dontsovcmc/waterius/Board/1.0-homemade/waterius-homemade-board.png

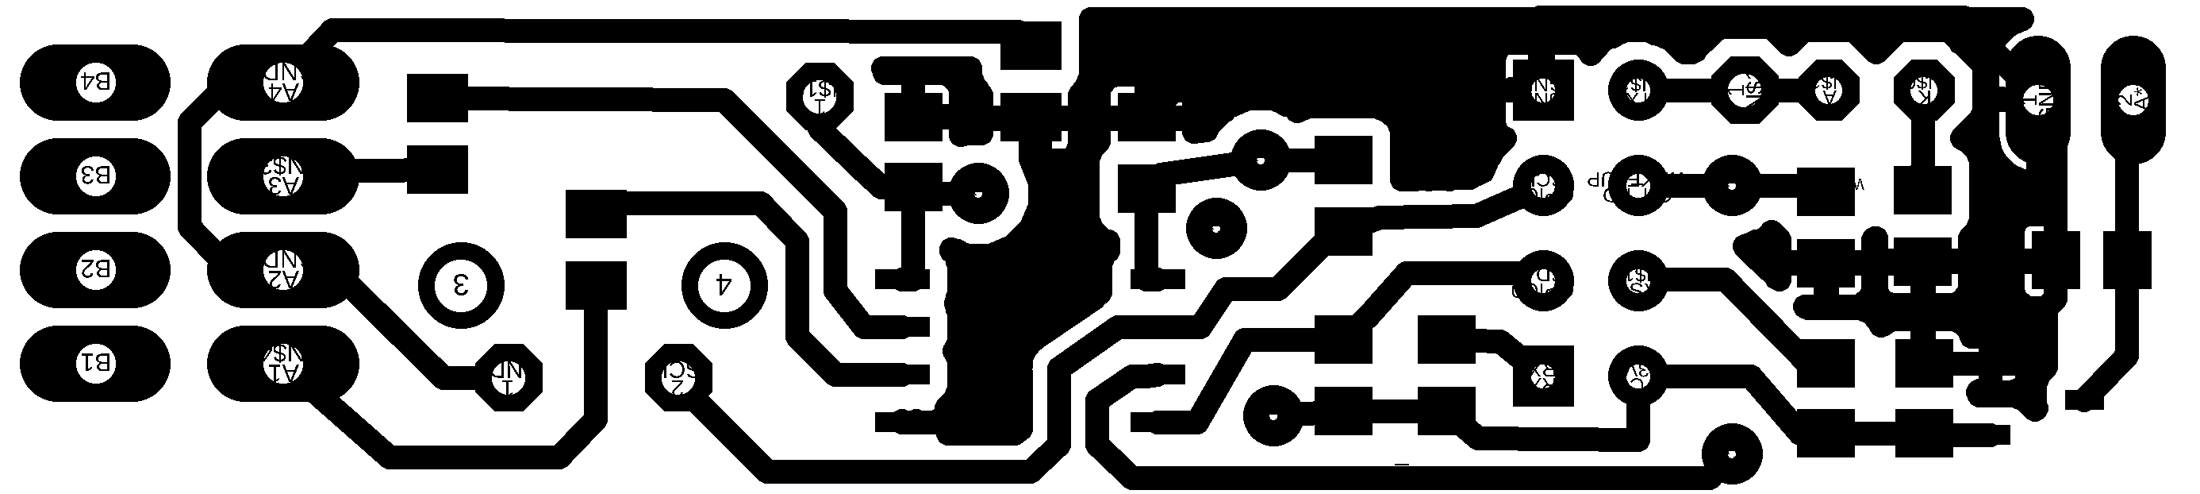
Board/1.0-homemade/waterius-homemade-board.png
