dontsovcmc/waterius/Board/2.0/waterius-factory-board2_top.jpg

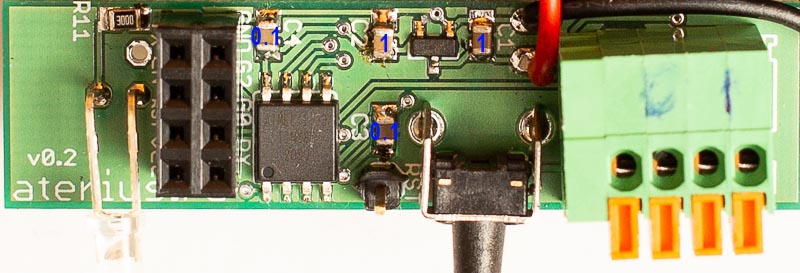
Board/2.0/waterius-factory-board2_top.jpg
