dontsovcmc/waterius/Board/3.0/waterius-factory-board3_top.jpg

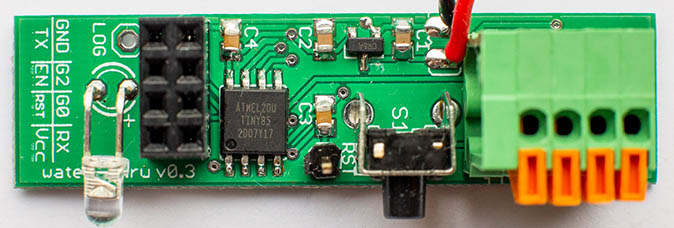
Board/3.0/waterius-factory-board3_top.jpg
