dontsovcmc/waterius/ESP8266/data/images/meter-cold-0.png

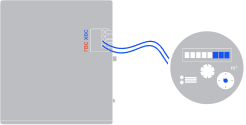
ESP8266/data/images/meter-cold-0.png
