dontsovcmc/waterius/ESP8266/data/images/meter-electro-0.png

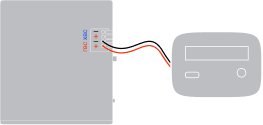
ESP8266/data/images/meter-electro-0.png
