dontsovcmc/waterius/ESP8266/data/images/meter-gas-0.png

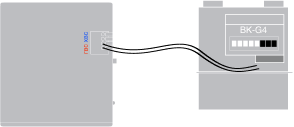
ESP8266/data/images/meter-gas-0.png
