dontsovcmc/waterius/files/11541426.png

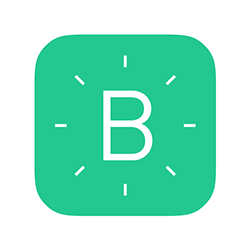
files/11541426.png
