dontsovcmc/waterius/files/esp8266-01s_mod.jpg

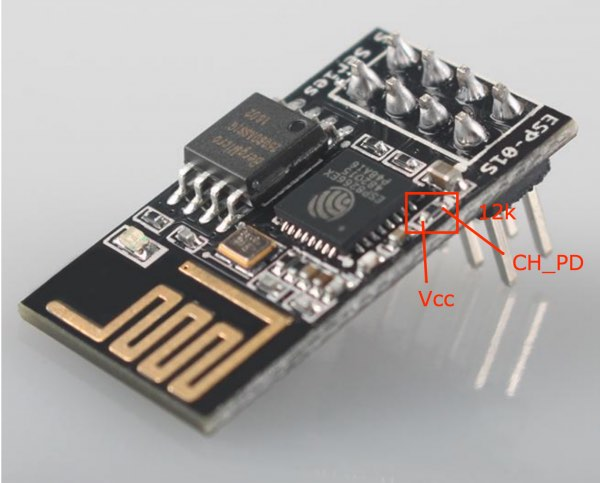
files/esp8266-01s_mod.jpg
