dontsovcmc/waterius/files/power.png

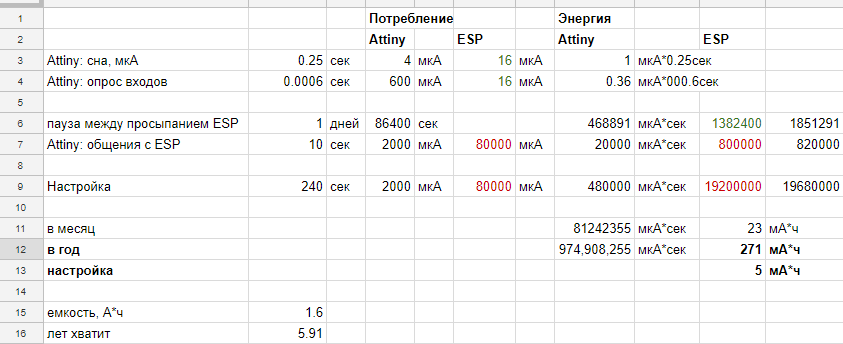
files/power.png
