dontsovcmc/waterius/files/qr.png

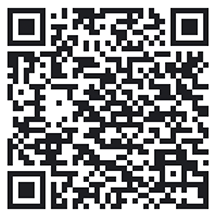
files/qr.png
