dontsovcmc/waterius/files/title.jpg

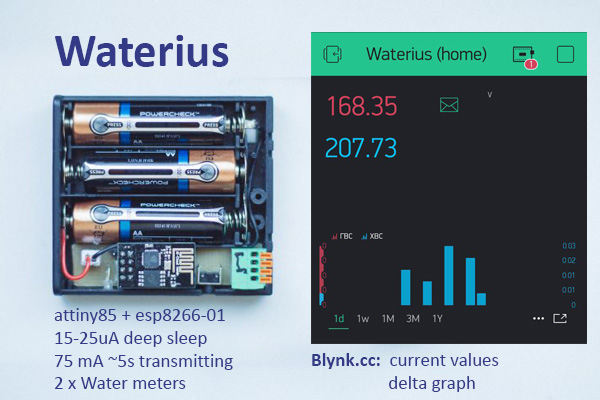
files/title.jpg
