dontsovcmc/waterius/files/top.jpg

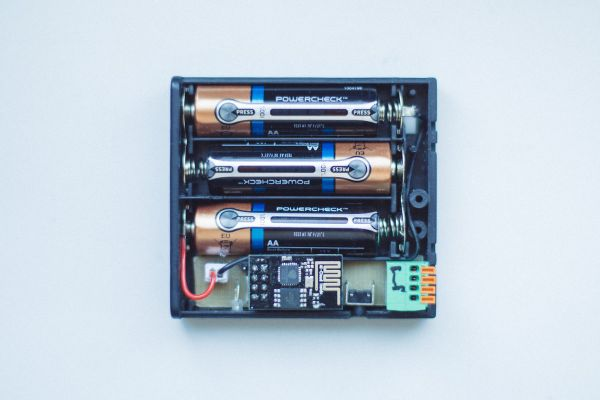
files/top.jpg
