dontsovcmc/waterius/files/step02.png

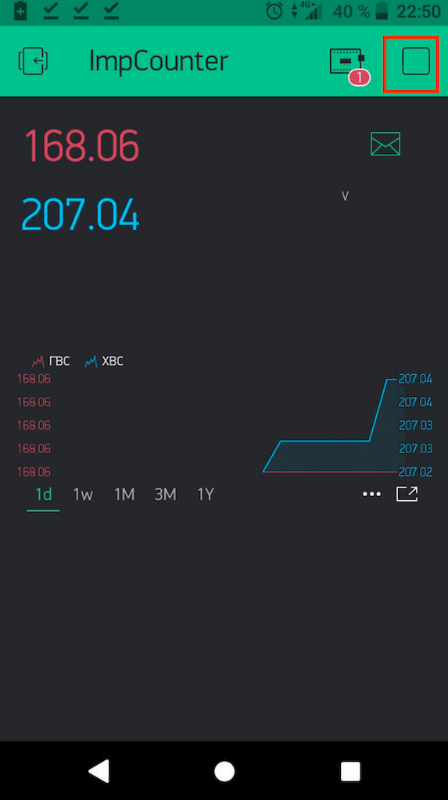
files/step02.png
