dontsovcmc/waterius/files/step04.png

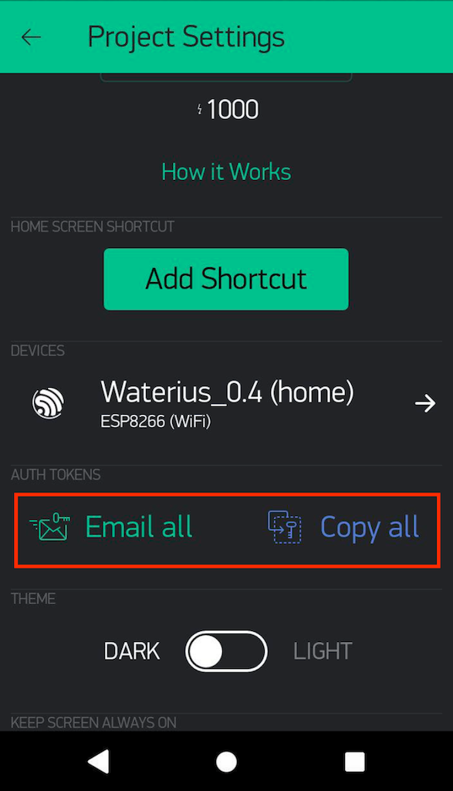
files/step04.png
