dontsovcmc/waterius/ESP8266/src/sync_time.cpp

#include "sync_time.h"
#include "Logging.h"
#include <IPAddress.h>
#include <WiFiUdp.h>
#include <ESP8266WiFi.h>
#include <time.h>

// Модуль основан на следующих модулях
// https://github.com/arduino-libraries/NTPClient/blob/master/NTPClient.cpp
// https://github.com/letscontrolit/ESPEasy/blob/mega/src/src/Helpers/ESPEasy_time.cpp
// https://github.com/arendst/Tasmota/blob/development/tasmota/tasmota_support/support_wifi.ino

#define START_VALID_TIME 1704067201UL // Jan 01 2024 00:00:01
#define DNS_TIMEOUT 1000              // 1 секунда
#define NTP_TIMEOUT 300               // обычно ответ приходит за 30-50 мсек
#define NTP_PORT 123
#define SEVENTY_YEARS 2208988800UL // от 1900 до 1970 в секундах
#define NSEC 1000000000UL
#define USEC 1000000UL
#define MSEC 1000UL
#define TIME_FORMAT "%FT%T%z"
#define UDP_PORT_ATTEMPTS 3
#define NTP_ATTEMPTS 5

const uint32_t NTP_PACKET_SIZE = 48;    // NTP time is in the first 48 bytes of message
uint8_t packet_buffer[NTP_PACKET_SIZE]; // Buffer to hold incoming & outgoing packets

/**
 * @brief Получает следующий ижентификатор в пуле серверов
 *
 * @return int
 */
int get_next_ntp_server_id()
{
    static int ntp_server_id = -1;
    // первый раз сервер выбирается случайным образом из пула
    // каждый следующий разу будет выбираться следующий в пуле
    if (ntp_server_id < 0)
    {
        ntp_server_id = random(0, 3);
    }
    else
    {
        ntp_server_id++;
        if (ntp_server_id > 3)
        {
            ntp_server_id = 0;
        }
    }
    return ntp_server_id;
}

/**
 * @brief Получает имя следующего в пуле сервера
 *
 * @return String имя сервера
 */
String get_next_ntp_server_name()
{
    int ntp_server_id = get_next_ntp_server_id();
    String ntp_server_name = String(ntp_server_id);
    ntp_server_name += F(".ru.pool.ntp.org");
    return ntp_server_name;
}

/**
 * @brief Открывает UDP порт для начала передачи
 *
 * @param udp класс для работы с UDP
 * @return true удалось открыть порт
 * @return false Не удалось открыть порт
 */
bool begin_udp_random_port(WiFiUDP &udp)
{
    unsigned int attempts = UDP_PORT_ATTEMPTS;

    do
    {
        long port = random(1025, 65535);
        if (udp.begin(port) != 0)
        {
            return true;
        }
    } while (attempts--);

    return false;
}

/**
 * @brief Парсинг ответа NTP сервера
 *
 * @param udp
 * @return uint64_t
 */
uint64_t get_ntp_response(WiFiUDP &udp)
{
    uint32_t begin_wait = millis();

    while (millis() - begin_wait < NTP_TIMEOUT)
    {
        uint32_t size = udp.parsePacket();
        uint32_t remote_port = udp.remotePort();

        if ((size >= NTP_PACKET_SIZE) && (remote_port == NTP_PORT))
        {
            udp.read(packet_buffer, NTP_PACKET_SIZE); // Read packet into the buffer
            udp.stop();

            if ((packet_buffer[0] & 0b11000000) == 0b11000000)
            {
                // Leap-Indicator: unknown (clock unsynchronized)
                // See: https://github.com/letscontrolit/ESPEasy/issues/2886#issuecomment-586656384
                LOG_ERROR(F("NTP: unsynced IP"));
                return false;
            }

            // convert four bytes starting at location 40 to a long integer
            // TX time is used here.
            uint32_t secs_since_1900 = (uint32_t)packet_buffer[40] << 24;
            secs_since_1900 |= (uint32_t)packet_buffer[41] << 16;
            secs_since_1900 |= (uint32_t)packet_buffer[42] << 8;
            secs_since_1900 |= (uint32_t)packet_buffer[43];
            if (0 == secs_since_1900) // No time stamp received
            {
                LOG_ERROR(F("NTP: No time stamp received"));
                return false;
            }

            uint32_t tmp_fraction = (uint32_t)packet_buffer[44] << 24;
            tmp_fraction |= (uint32_t)packet_buffer[45] << 16;
            tmp_fraction |= (uint32_t)packet_buffer[46] << 8;
            tmp_fraction |= (uint32_t)packet_buffer[47];
            uint32_t fraction = (((uint64_t)tmp_fraction) * NSEC) >> 32;

            uint64_t ntp_nanos = (((uint64_t)secs_since_1900) - SEVENTY_YEARS) * NSEC + fraction;

            uint32_t total_delay = millis() - begin_wait;

            // compensate for the delay by adding half the total delay
            uint32_t delay_compensation = total_delay / 2;

            LOG_INFO(F("NTP: NTP replied: delay ") << total_delay << F(" mSec"));

            ntp_nanos += (uint64_t)delay_compensation * (NSEC / MSEC);

            return ntp_nanos;
        }
        delay(10);
    }
    // Timeout.
    LOG_ERROR(F("NTP: No reply from NTP server"));
    udp.stop();
    return 0;
}

/**
 * @brief Формирование и отправка запроса на получение времени с сервера
 *
 * @param udp
 * @param ntp_server_ip
 * @return true
 * @return false
 */
bool send_ntp_request(WiFiUDP &udp, IPAddress &ntp_server_ip)
{
    while (udp.parsePacket() > 0) // Discard any previously received packets
    {
        yield();
    }

    memset(packet_buffer, 0, NTP_PACKET_SIZE);
    packet_buffer[0] = 0b11100011; // LI, Version, Mode
    packet_buffer[1] = 0;          // Stratum, or type of clock
    packet_buffer[2] = 6;          // Polling Interval
    packet_buffer[3] = 0xEC;       // Peer Clock Precision
    packet_buffer[12] = 49;
    packet_buffer[13] = 0x4E;
    packet_buffer[14] = 49;
    packet_buffer[15] = 52;

    if (udp.beginPacket(ntp_server_ip, NTP_PORT) == 0) // NTP requests are to port 123
    {
        udp.stop();
        return false;
    }

    yield();

    udp.write(packet_buffer, NTP_PACKET_SIZE);
    udp.endPacket();
    return true;
}

/**
 * @brief Возвращает текущее время с сервера NTP в наносекундах
 *
 * @param ntp_server_name  имя сервера NTP
 * @return uint_64t  время с сервера NTP в наносекундах
 */
uint64_t get_ntp_nanos(const String &ntp_server_name)
{
    IPAddress ntp_server_ip;

    if (WiFi.hostByName(ntp_server_name.c_str(), ntp_server_ip, DNS_TIMEOUT) != 1)
    {
        LOG_ERROR(F("NTP: Unable to resolve ") << ntp_server_name);
        return 0;
    }

    LOG_INFO(F("NTP: NtpServer ") << ntp_server_name << F(" IP ") << ntp_server_ip.toString());

    yield();

    WiFiUDP udp;

    if (!begin_udp_random_port(udp))
    {
        LOG_ERROR(F("NTP: Unable to open udp port "));
        return 0;
    }

    yield();

    if (!send_ntp_request(udp, ntp_server_ip))
    {
        LOG_ERROR(F("NTP: Unable to send"));
        return 0;
    }

    yield();

    uint64_t ntp_nanos = get_ntp_response(udp);

    yield();

    return ntp_nanos;
}

/**
 * @brief Синхронизирует время c указанным сервером
 *
 * @param ntp_server_name имя сервера
 * @return true время синхронизировано
 * @return false время НЕ синхронизировано
 */
bool sync_ntp_time(const String &ntp_server_name)
{
    struct timeval tv;
    tv.tv_sec = START_VALID_TIME;
    tv.tv_usec = 0;
    settimeofday(&tv, NULL);

    uint32_t start_time = millis();

    uint64_t ntp_nanos = get_ntp_nanos(ntp_server_name);

    tv.tv_sec = ntp_nanos / NSEC;
    tv.tv_usec = (ntp_nanos % NSEC) / 1000;

    if (is_valid_time(tv.tv_sec))
    {
        settimeofday(&tv, NULL);
        LOG_INFO(F("NTP: Time synced ") << millis() - start_time << F(" msec"));
        LOG_INFO(F("NTP: Current time ") << get_current_time());
        return true;
    }
    else
    {
        LOG_ERROR(F("NTP: Unable to sync time"));
        return false;
    }
}

/**
 * @brief Синхронизация времени по протоколу NTP
 *
 * @return true время синхронизировано
 * @return false время НЕ синхронизировано
 */
bool sync_ntp_time()
{
    uint32_t start_time = millis();
    LOG_INFO(F("NTP: Sync time..."));
    String ntp_server_name;

    int attempts = NTP_ATTEMPTS;

    do
    {
        LOG_INFO(F("NTP: Attempt #") << NTP_ATTEMPTS - attempts + 1 << F(" from ") << NTP_ATTEMPTS);
        ntp_server_name = get_next_ntp_server_name();
        if (sync_ntp_time(ntp_server_name))
        {
            LOG_INFO(F("NTP: Time successfully synced. Total time spent ") << millis() - start_time << F(" msec"));
            return true;
        };
    } while (--attempts);

    LOG_ERROR(F("NTP: Time could not synced. Total time spent ") << millis() - start_time << F(" msec"));
    return false;
}

/**
 * @brief Синхронизирует время по настройкам пользователя
 *
 * @param sett настройки устройства
 * @return true время синхронизировано
 * @return false время НЕ синхронизировано
 */
bool sync_ntp_time(const Settings &sett)
{

    String ntp_server = sett.ntp_server;

    if (sett.ntp_server[0] && !ntp_server.equalsIgnoreCase(String(DEFAULT_NTP_SERVER))) // проверяем что сервер указан и не равняется по умолчанию
    {
        // Пробуем получить время с пользовательского сервера
        if (sync_ntp_time(ntp_server))
        {
            return true;
        }
    }
    // если не удалось с пользовательского сервера получить время
    // то берем время по серврам из пула
    return sync_ntp_time();
}

/**
 * @brief Получает текущее время
 *
 * @return строка с временем в формате C
 */
String get_current_time()
{
    char buf[100];
    time_t now = time(nullptr);
    struct tm timeinfo;
    gmtime_r(&now, &timeinfo);
    // ISO8601 date time string format (2019-11-29T23:29:55+0800).
    strftime(buf, sizeof(buf), TIME_FORMAT, &timeinfo);
    return String(buf);
}

/**
 * @brief Проверка валидно ли время,
 * дата должна быть больше чем 1 Января 2020 года
 *
 * @param time
 * @return true время валидно
 * @return false время невалидно
 */
bool is_valid_time(time_t time)
{
    return time > START_VALID_TIME;
}
