dontsovcmc/waterius/Attiny85/src/counter.h

#ifndef _COUNTER_h
#define _COUNTER_h

#include <Arduino.h>
#include <avr/wdt.h>
#include <avr/power.h>
#include "Power.h"

#if WATERIUS_MODEL == WATERIUS_MODEL_1 
    // Значения компаратора с pull-up резистором ~30кОм.
    // На входе последовательно 3к3 + 300ом на GND.
    // 0   - 104 - замыкание
    // 1к5 - 130 - намур замкнут
    // 2к2 - 154
    // 3к0 - 171
    // 4к5 - 195
    // 5к5 - 230 - намур разомкнут
    #define LIMIT_CLOSED 115       // < 115 - замыкание
    #define LIMIT_NAMUR_CLOSED 150 // < 150 - намур замкнут
    #define LIMIT_NAMUR_OPEN 800   // < 800 - намур разомкнут
                                   // > - обрыв
#endif
#if WATERIUS_MODEL == WATERIUS_MODEL_2 
    // Значения компаратора с pull-up резистором ~30кОм.
    // : замкнут (0 ом) - намур-замкнут (1к5) - намур-разомкнут (5к5) - обрыв линии
    // на входе 1кОм, подтяжка значит 33кОм
    // : 30  - 72 - 170 - 1000

    // Значения компаратора с pull-up резистором ~30кОм.
    // На входе последовательно 1кОм
    // 0   - 42 - замыкание
    // 1к5 - 78 - намур замкнут
    // 2к2 - 100 
    // 3к0 - 116
    // 4к5 - 150 
    // 5к5 - 170 - намур разомкнут

    #define LIMIT_CLOSED 50        // < 50 - замыкание
    #define LIMIT_NAMUR_CLOSED 100 // < 150 - намур замкнут
    #define LIMIT_NAMUR_OPEN 800   // < 800 - намур разомкнут
                                   // > - обрыв
#endif

#define DELAY_PIN_READY_US 30
#define IMPULSE_CONFIRM_MS 50  // подтверждение импульса: пауза перед повторным чтением входа

enum CounterState
{
    CLOSE,
    NAMUR_CLOSE,
    NAMUR_OPEN,
    OPEN
};

enum CounterType 
{
    NAMUR,
    DISCRETE,
    ELECTRONIC,
    HALL,
    NONE = 0xFF
};

enum class CounterEvent
{
    NONE,
    FRONT,
    TIME,
};


struct CounterB
{
    uint8_t         _pin;       // дискретный вход
    uint8_t         _power;     // питание датчика
    uint8_t         _apin;      // номер аналогового входа

    uint8_t         on_time;    // для того чтобы светодиод во время настройки загорался дольше чем на 2 сек (чтобы не бомбить i2c)
    uint8_t         off_time;   // время в разомкнутом состоянии
    uint8_t         levels;     // уровни входа
    bool            on_pulse;   // 
    bool            active;     // идет потребление через счетчик

    uint16_t        adc;        // уровень замкнутого входа
    CounterState    state;      // состояние входа
    CounterType     type;       // тип выхода счетчика

    explicit CounterB(uint8_t pin, uint8_t apin = 0, uint8_t power = (uint8_t)-1)
        : _pin(pin), _power(power), _apin(apin), on_time(0), off_time(0), adc(0), state(CounterState::CLOSE), type(CounterType::NAMUR)
    {
        set_type(type);
    }

    void set_type(CounterType new_type)
    {
        if ((type == CounterType::HALL) && (_power != (uint8_t)-1)) {
            DDRB &= ~_BV(_power);       // Пин питания датчика возвращаем на вход
        }
        type = new_type;
        if ((type == CounterType::HALL) && (_power == (uint8_t)-1))
        {
            type = CounterType::NONE;
        }
        switch (type)
        {
            case CounterType::ELECTRONIC:
                PORTB |= _BV(_pin);                 // Включить pull-up
		        PCMSK |= _BV(_pin);                 // Включем прерывание по фронту
            case CounterType::DISCRETE:
            case CounterType::NAMUR:
                DDRB &= ~_BV(_pin);                 // Вход
                break;
            case CounterType::HALL:
                DDRB &= ~_BV(_pin);                 // Вход
                DDRB |= _BV(_power);                // Пин питания датчика ставим на выход
                PORTB &= ~_BV(_pin);                // Отключить pull-up
                PORTB |= _BV(_power);               // Включить питание
                delayMicroseconds(DELAY_PIN_READY_US); // Задержка на включение датчика
                state = bit_is_set(PINB, _pin) ? CounterState::OPEN : CounterState::CLOSE;
                active = false;
                break;
            case CounterType::NONE:
                break;
        }
    }

    inline uint16_t aRead()
    {
	    power_adc_enable();
	    adc_enable();
        return analogRead(_apin);
    }

    bool electronic(CounterEvent event)
    {
        if (on_time)
            on_time -= 1;

        state = bit_is_set(PINB, _pin) ? CounterState::OPEN : CounterState::CLOSE;
        if (state == CounterState::CLOSE)
        {
            // Замкнут
            if (!on_pulse)
            {
                // Начало импульса
                on_time = 10;
                off_time = 0;
                adc = aRead();
                on_pulse = true;
                return true;
            }
        }
        else
        {
            // Разомкнут
            on_pulse = false;
        }
        return false;
    }

    bool hall(CounterEvent event)
    {
        PORTB |= _BV(_power);               // Включить питание
        delayMicroseconds(DELAY_PIN_READY_US); // Задержка на включение датчика
        CounterState new_state = bit_is_set(PINB, _pin) ? CounterState::OPEN : CounterState::CLOSE;
        if (new_state != state) 
        {
            state = new_state;
            if (!active) 
            {
                active = true;
                PCMSK |= _BV(_pin);         // Включем прерывание по фронту
            }
        }
        else if (!active)
        {
            PCMSK &= ~_BV(_pin);            // Отключем прерывание по фронту
            PORTB &= ~_BV(_power);          // Отключить питание
        }
        if (state == CounterState::CLOSE)
        {
            // Замкнут
            off_time = 0;
            if (on_time == 0)
            {
                // Начало импульса
                on_time = 1;
                adc = aRead();
                return true;
            }
            else
            {
                // Продолжение
                if (on_time < 200)
                {
                    // Увеличиваем счетчик времени в замкнутом состоянии
                    on_time += event == CounterEvent::TIME ? 10 : 1;
                } 
                else
                {
                    // Через 5 секунд отсутствия импульсов считаем что потребление закончилось
                    active = false;
                }
            }
        }
        else
        {
            // Разомкнут
            on_time = 0;
            // Увеличиваем счетчик времени в разомкнутом состоянии
            if (off_time < 200)
            {
                off_time += event == CounterEvent::TIME ? 10 : 1;
            }
            else
            {
                // Через 5 секунд отсутствия импульсов считаем что потребление закончилось
                active = false;
            }
        }
        return false;
    }

    // Одно чтение входа: включить pull-up, измерить (ADC для NAMUR), вернуть "замкнуто?"
    inline bool is_closed()
    {
        PORTB |= _BV(_pin);                 // Включить pull-up
        delayMicroseconds(DELAY_PIN_READY_US);
        if (type == CounterType::NAMUR)
        {
            uint16_t a = aRead();
            state = value2state(a);
            if (state == CounterState::CLOSE || state == CounterState::NAMUR_CLOSE)
            {
                adc = a;
            }
        }
        else
        {
            state = bit_is_set(PINB, _pin) ? CounterState::OPEN : CounterState::CLOSE;
            if ((state == CounterState::CLOSE) && !on_pulse)
            {
                adc = aRead();
            }
        }
        PORTB &= ~_BV(_pin);                // Отключить pull-up
        return (state == CounterState::CLOSE || state == CounterState::NAMUR_CLOSE);
    }

    bool discrete(CounterEvent event)
    {
        /*
        Вызывается раз в 250мс.
        Импульс счетчика длится дольше 100мс, а вход опрашивается раз в 250мс,
        поэтому короткий импульс можно пропустить между опросами. Чтобы поднять
        чувствительность без учащения опроса: при первом замыкании после паузы
        ждём ~50мс и проверяем ещё раз. Если вход всё ещё замкнут - это импульс
        (засчитываем сразу), иначе это глитч < 50мс - игнорируем.
        Конец импульса детектируем как и раньше: 3 разомкнутых состояния подряд.
        */
        if (event == CounterEvent::FRONT)
            return false;

        bool closed = is_closed();
        levels = (levels << 1) | (closed & 1);   // нужен для детекта конца импульса

        if (on_time)
            on_time -= 1;

        if (on_pulse)
        {
            if (!on_time)
                on_time = 1;                      // держим пока on_pulse
            if ((levels & 0x07) == 0x00)          // 3 разомкнуто подряд - конец импульса
            {
                on_pulse = false;
            }
        }
        else
        {
            if (closed)                           // первое замыкание после паузы
            {
                for (uint8_t i = 0; i < IMPULSE_CONFIRM_MS; i++)
                {
                    wdt_reset();
                    delayMicroseconds(1000);      // пауза ~1мс
                }
                if (is_closed())                  // через ~50мс всё ещё замкнут?
                {
                    on_pulse = true;
                    on_time = 10;                 // ~2.5с подсветка светодиода
                    return true;                  // засчитать импульс
                }
                // иначе глитч < 50мс - игнорируем, флаг не поднимаем
            }
        }

        return false;
    }

    bool is_impuls(CounterEvent event = CounterEvent::NONE)
    {
        switch (type) 
        {
            case CounterType::ELECTRONIC:
                return electronic(event);
            case CounterType::HALL:
                return hall(event);
            case CounterType::NAMUR:
            case CounterType::DISCRETE:
                return discrete(event);
            case CounterType::NONE:
            default:
                return false;
        }
    }

    // Возвращаем текущее состояние входа
    inline CounterState value2state(uint16_t value)
    {
        if (value < LIMIT_CLOSED)
        {
            return CounterState::CLOSE;
        }
        else if (value < LIMIT_NAMUR_CLOSED)
        {
            return CounterState::NAMUR_CLOSE;
        }
        else if (value < LIMIT_NAMUR_OPEN)
        {
            return CounterState::NAMUR_OPEN;
        }
        else
        {
            return CounterState::OPEN;
        }
    }
};

#endif
