dontsovcmc/waterius/Attiny85/src/Setup.h

#ifndef _WATERIUS_SETUP_h
#define _WATERIUS_SETUP_h

#include <Arduino.h>

/*
    Классический Ватериус
 */
#define WATERIUS_MODEL_1 0

/*
    Ватериус 2
*/
#define WATERIUS_MODEL_2 2


/*
    Включение логирования
    3 pin TX -> RX (TTL-USB 3.3 или 5в), 9600 8N1
    При логировании не работает счетчик2 на 3-м пине (Вход 2).

    #define LOG_ON
*/

/*
    Включение отладки сигнала со счетчиков на пин питания ESP
    
    #define COUNTER_DEBUG
*/

#ifndef LOG_ON
#define LOG_BEGIN(x)
#define LOG(x)
#else
#undef LOG_BEGIN
#undef LOG

// TinyDebugSerial на PB3 только в attiny85, 1MHz
#include "TinyDebugSerial.h"
#define LOG_BEGIN(x) DDRB |= _BV(3); mySerial.begin(x)
#define LOG(x)                \
    mySerial.print(millis()); \
    mySerial.print(F(" : ")); \
    mySerial.println(x);
#endif

/*
   1 минута примерно равна 240 пробуждениям
*/
#define ONE_MINUTE 240L

/*
    Период отправки данных на сервер, мин.
*/
#define WAKEUP_PERIOD_DEFAULT 15L * ONE_MINUTE


/*
    Аварийное отключение, если ESP зависнет и не пришлет команду "сон".
*/
#define WAIT_ESP_MSEC 120000UL

/*
    Сколько милисекунд пользователь может
    настраивать ESP. Если не закончил, питание ESP выключится.
*/
#define SETUP_TIME_MSEC 600000UL

/*
    время долгого нажатия кнопки, милисекунд
*/
#define LONG_PRESS_MSEC 2000

/*
    пауза мс перед переходом ESP в сон (чтобы успел отключиться)
*/
#define DELAY_SENT_SLEEP 20000
       

struct Data
{
    uint32_t value0;
    uint32_t value1;
};

struct CounterTypes
{
    uint8_t type0; // тип входа
    uint8_t type1;
};

struct ADCLevel
{
    uint16_t adc0;
    uint16_t adc1;
};

struct Config
{
    uint8_t setup_started_counter;      // Включение режима настройки
    uint8_t resets;                     // Количество перезагрузок
    uint8_t model;                      // Модификация: 0 - Обычный Ватериус, 2 - Ватериус2
    CounterTypes types;                 // Типы входов счетчиков
};

struct Header
{

    /*
    Версия прошивки
    */
    uint8_t version;

    /*
    Причина перезагрузки (регистр MCUSR datasheet 8.5.1):
         0001 - PORF: Power-on Reset Flag. Напряжение питания было низкое или 0.
         0010 - EXTRF: External Reset Flag. Пин ресет был в низком уровне.
         0100 - BORF: Brown-out Reset Flag. Напряжение питание было ниже требуемого.
         1000 - WDRF: Watchdog Reset Flag. Завершение работы таймера.

    8  - 1000 - WDRF
    9  - 1001 - WDRF + PORF
    10 - 1010 - WDRF + EXTRF
    */
    uint8_t service: 6;      // биты 0-5: причина перезагрузки
    uint8_t on_pulse0: 1;    // бит 6: импульс на входе 0
    uint8_t on_pulse1: 1;    // бит 7: импульс на входе 1

    /*
    Напряжение питания Attiny85 в мВ
    */
    uint16_t voltage;

    /*
    Для совместимости с 0.10.0.
    */
    uint8_t reserved2;

    /*
    Конфигурация
    */
    Config config;

    /*
    Текущие данные
    */
    Data data;           // 8 байт
    ADCLevel adc;        // 4 байта

    // HEADER_DATA_SIZE

    uint8_t crc;
    uint8_t reserved3;
}; // 24 байт

#define HEADER_DATA_SIZE 22

#define TX_BUFFER_SIZE HEADER_DATA_SIZE + 2

#define ASSERT_CONCAT_(a, b) a##b
#define ASSERT_CONCAT(a, b) ASSERT_CONCAT_(a, b)
#define ct_assert(e) enum { ASSERT_CONCAT(assert_line_, __LINE__) = 1/(!!(e)) }

ct_assert(sizeof(Header)==24);

#endif
