dontsovcmc/waterius/ESP8266/src/portal/resources.h

#ifndef __RESOURCES_H_
#define __RESOURCES_H_

#include <pgmspace.h>

// Здесь расположены параметры, которые указаны в html страницах веб портала и парсятся бэкендом 
// 
static const char PARAM_VERSION[] PROGMEM = "version";
static const char PARAM_VERSION_ESP[] PROGMEM = "version_esp";
static const char PARAM_WATERIUS_HOST[] PROGMEM = "waterius_host";
static const char PARAM_WATERIUS_EMAIL[] PROGMEM = "waterius_email";
static const char PARAM_HTTP_URL[] PROGMEM = "http_url";
static const char PARAM_MQTT_HOST[] PROGMEM = "mqtt_host";
static const char PARAM_MQTT_PORT[] PROGMEM = "mqtt_port";
static const char PARAM_MQTT_LOGIN[] PROGMEM = "mqtt_login";
static const char PARAM_MQTT_PASSWORD[] PROGMEM = "mqtt_password";
static const char PARAM_MQTT_TOPIC[] PROGMEM = "mqtt_topic";
static const char PARAM_IP[] PROGMEM = "ip";
static const char PARAM_GATEWAY[] PROGMEM = "gateway";
static const char PARAM_MASK[] PROGMEM = "mask";
static const char PARAM_MAC_ADDRESS[] PROGMEM = "mac_address";
//static const char PARAM_WAKEUP_PER_MIN[] PROGMEM = "wakeup_per_min"; // use s_period_min from ha/resources.h
static const char PARAM_COMPANY[] PROGMEM = "company";
static const char PARAM_PLACE[] PROGMEM = "place";
static const char PARAM_MQTT_AUTO_DISCOVERY[] PROGMEM = "mqtt_auto_discovery";
static const char PARAM_MQTT_DISCOVERY_TOPIC[] PROGMEM = "mqtt_discovery_topic";
static const char PARAM_MQTT_RETAIN[] PROGMEM = "mqtt_retain";
static const char PARAM_NTP_SERVER[] PROGMEM = "ntp_server";
static const char PARAM_SSID[] PROGMEM = "ssid";
static const char PARAM_PASSWORD[] PROGMEM = "password";
static const char PARAM_WIFI_PHY_MODE[] PROGMEM = "wifi_phy_mode";

static const char PARAM_WATERIUS_ON[] PROGMEM = "waterius_on";
static const char PARAM_HTTP_ON[] PROGMEM = "http_on";
static const char PARAM_MQTT_ON[] PROGMEM = "mqtt_on";
static const char PARAM_DHCP_OFF[] PROGMEM = "dhcp_off";

static const char PARAM_INPUT[] PROGMEM = "input";
static const char PARAM_CHANNEL_START[] PROGMEM = "channel_start";
static const char PARAM_SERIAL[] PROGMEM = "serial";
static const char PARAM_COUNTER_NAME[] PROGMEM = "counter_name";
static const char PARAM_COUNTER0_NAME[] PROGMEM = "counter0_name";
static const char PARAM_COUNTER1_NAME[] PROGMEM = "counter1_name";
static const char PARAM_COUNTER_TYPE[] PROGMEM = "counter_type";
static const char PARAM_COUNTER0_TYPE[] PROGMEM = "counter0_type";
static const char PARAM_COUNTER1_TYPE[] PROGMEM = "counter1_type";
static const char PARAM_COUNTER_IMG[] PROGMEM = "counter_img";
static const char PARAM_FACTOR[] PROGMEM = "factor";
static const char PARAM_ASTERICS[] PROGMEM = "********";


static const char PARAM_WIZARD[] PROGMEM = "wizard";
static const char PARAM_TRUE[] PROGMEM = "true";

static const char ERROR_LENGTH_ERROR[] PROGMEM = "Превышена длина поля";
static const char ERROR_VALUE[] PROGMEM = "Неверное значение";
static const char ERROR_ATTINY_ERROR[] PROGMEM = "Ошибка связи с attiny";
static const char ERROR_EMPTY[] PROGMEM = "Значение не может быть пустым";

// не из конфигурации
static const char PARAM_BUILD_DATE_TIME[] PROGMEM = "build_date_time";
static const char PARAM_FS_SIZE[] PROGMEM = "fs_size";
static const char PARAM_FS_FREE[] PROGMEM = "fs_free";

static const char PARAM_WIFI_CONNECT_STATUS[] PROGMEM = "wifi_connect_status";

// logging
static const char PARAM_SAVED[] PROGMEM = "Saved: ";
static const char PARAM_SAVED0[] PROGMEM = "Saved input0: ";
static const char PARAM_SAVED1[] PROGMEM = "Saved input1: ";

#endif
