dontsovcmc/waterius/ESP8266/src/master_i2c.h

#ifndef _MASTERI2C_h
#define _MASTERI2C_h

#include <Arduino.h>
#include "setup.h"

/*
Номера пинов линии i2c.
*/
#if WATERIUS_MODEL == WATERIUS_MODEL_1      // MODEL_CLASSIC (ESP-01)
#define SDA_PIN 0
#define SCL_PIN 2
#endif
#if WATERIUS_MODEL == WATERIUS_MODEL_2    // MODEL_2 (NodeMCU/ESP-12F)
#define SDA_PIN 4
#define SCL_PIN 5
#endif


#define INIT_ATTINY_CRC 0xFF

// Класс для синхронизации запросов к i2c, которые могут быть из разных потоков в AsyncWebServer
// В ESP отсутствуют мьютексы, поэтому будем считать, что это проще сдела
class BusyGuard {
    volatile bool& busy;
public:
    BusyGuard(volatile bool& flag) : busy(flag) {
        while (true) {
            noInterrupts();
            if (!busy) {
                busy = true;
                interrupts();
                break;
            }
            interrupts();
            yield();
        }
    }
    ~BusyGuard() {
        busy = false;
    }
    BusyGuard(const BusyGuard&) = delete;
    BusyGuard& operator=(const BusyGuard&) = delete;
};

/*
Данные принимаемые от Attiny
*/
struct AttinyData
{
    // Header
    uint8_t version;    // Версия ПО Attiny
    uint8_t service;    // Причина загрузки Attiny (биты 0-5), биты 6-7 = on_pulse флаги
    bool on_pulse0;
    bool on_pulse1;
    uint8_t reserved5 = 0;
    uint16_t voltage;   // Напряжение питания в мВ
    uint8_t reserved;   // Для совместимости
    uint8_t setup_started_counter;
    uint8_t resets;
    uint8_t model;         // WATERIUS_MODEL_1 или  WATERIUS_MODEL_2
    uint8_t counter_type0; // Тип входа, вход 0
    uint8_t counter_type1; //           вход 1
    uint32_t impulses0;    // Импульсов, канал 0
    uint32_t impulses1;    //           канал 1
    uint16_t adc0;         // Уровень,   канал 0
    uint16_t adc1;         //           канал 1

    // HEADER_DATA_SIZE

    uint8_t crc = 0; // Всегда в конце структуры данных
    uint8_t reserved2 = 0;
    // Кратно 16bit https://github.com/esp8266/Arduino/issues/1825
};

uint8_t crc_8(const unsigned char *input_str, size_t num_bytes, uint8_t crc = 0);

class MasterI2C
{
    uint8_t init_crc = 0xFF;
    volatile bool i2c_busy;

protected:
    bool getUint(uint32_t &value, uint8_t &crc);
    bool getUint16(uint16_t &value, uint8_t &crc);
    bool getByte(uint8_t &value, uint8_t &crc);
    bool sendData(uint8_t *buf, size_t size);

    bool getByte(uint8_t *value, uint8_t &crc);
    bool getBytes(uint8_t *value, uint8_t count, uint8_t &crc);

public:
    MasterI2C();
    void begin();
    void end();
    bool sendCmd(uint8_t cmd);
    bool getMode(uint8_t &mode);
    bool getAttinyData(AttinyData &data);
    bool setWakeUpPeriod(uint16_t per);
    bool setCountersType(const uint8_t type0, const uint8_t type1);
    bool setTransmitMode();
    bool setSetupMode();
    bool setSleep();
    bool extendWakeUp();
    bool updateVoltage();
};

#endif
