dontsovcmc/waterius/ESP8266/src/ha_discovery.h

/**
 * @file home_assistant.h
 * @brief содерждит функции для формирования топиков MQTT для автоматического добавления в HomeAssistant
 * https://www.home-assistant.io/integrations/mqtt/#mqtt-discovery
 * 
 * @version 0.1
 * @date 2023-01-18
 *
 * @copyright Copyright (c) 2023
 *
 */
#ifndef HADISCOVERY_H_
#define HADISCOVERY_H_

#include "master_i2c.h"
#include <PubSubClient.h>

extern void publish(PubSubClient &mqtt_client, String &topic, String &payload);
extern void publish_discovery(PubSubClient &mqtt_client, String &topic, const SlaveData &data, bool single_topic);
extern void clean_discovery(PubSubClient &mqtt_client, String &topic);

#endif
