dontsovcmc/waterius/ImpCounterESP/src/SetupAP.cpp

#include "SetupAP.h"
#include "Logging.h"
#include <ESP8266WiFi.h>
#include <DNSServer.h>            // Local DNS Server used for redirecting all requests to the configuration portal
#include <ESP8266WebServer.h>     // Local WebServer used to serve the configuration portal
#include <WiFiClient.h>
#include <EEPROM.h>

#define AP_NAME "ImpulsCounter_0.3"


void setup_ap(Settings &sett, const SlaveData &data) 
{
	// Пользователь нажал кнопку - запускаем веб сервер
	LOG_NOTICE( "ESP", "I2C-begined: mode SETUP" );
	LOG_NOTICE( "WIF", "User requested captive portal" );
	WiFi.disconnect( true );
	WiFiManager wifiManager;
	
	IPAddressParameter param_ip("ip", "static IP", IPAddress(sett.ip));
	wifiManager.addParameter( &param_ip );
	IPAddressParameter param_subnet( "subnet", "subnet",  IPAddress(sett.subnet));
	wifiManager.addParameter( &param_subnet );
	IPAddressParameter param_gw( "gw", "gateway",  IPAddress(sett.gw));
	wifiManager.addParameter( &param_gw );

	WiFiManagerParameter param_key( "key", "key",  sett.key, KEY_LEN );
	wifiManager.addParameter( &param_key );
	WiFiManagerParameter param_hostname( "host", "host",  sett.hostname, HOSTNAME_LEN );
	wifiManager.addParameter( &param_hostname );

	FloatParameter param_value0_start( "value0", "value0",  sett.value0_start);
	wifiManager.addParameter( &param_value0_start );
	FloatParameter param_value1_start( "value1", "value1",  sett.value1_start);
	wifiManager.addParameter( &param_value1_start );

	LongParameter param_litres_per_imp( "factor", "factor",  sett.liters_per_impuls);
	wifiManager.addParameter( &param_litres_per_imp );

	// Start the portal with the SSID 
	wifiManager.startConfigPortal( AP_NAME );
	LOG_NOTICE( "WIF", "Connected to wifi" );

	// Get all the values that user entered in the portal and save it in EEPROM

	sett.ip = param_ip.getValue();
	sett.subnet = param_subnet.getValue();
	sett.gw = param_gw.getValue();
	
	strncpy(sett.key, param_key.getValue(), KEY_LEN);
	strncpy(sett.hostname, param_hostname.getValue(), HOSTNAME_LEN);

	sett.value0_start = param_value0_start.getValue();
	sett.value1_start = param_value1_start.getValue();
	sett.liters_per_impuls = param_litres_per_imp.getValue();

	sett.impules0_start = data.impulses0;
	sett.impules1_start = data.impulses1;

	LOG_NOTICE( "DAT", "impulses0_start=data.impulses0=" << sett.impules0_start );
	LOG_NOTICE( "DAT", "impulses1_start=data.impulses1=" << sett.impules1_start );

	sett.crc = 1239;
	storeConfig(sett);
}
