dontsovcmc/waterius/ImpCounterESP/MasterI2C.h

#ifndef _MASTERI2C_h
#define _MASTERI2C_h

#include <Arduino.h>

#define I2C_SLAVE_ADDR 10

struct SlaveStats {
	uint16_t bytesReady;
	uint16_t masterWakeEvery;
	uint16_t measurementEvery;
	uint8_t bytesPerMeasurement;
	uint8_t deviceID;
	uint8_t numberOfSensors;
};


class MasterI2C
{
 protected:
	 void gotoFirstByte();
	 byte getNextByte();
	 uint16_t getUint();
	 uint8_t getByte();

 public:
	 void begin();
	 void sendCmd( const char cmd );
	 uint16_t getSlaveStorage( byte* storage, const uint16_t maxStorageSize, const uint16_t bytesToFetch );
	 SlaveStats getSlaveStats();
};


#endif
