dontsovcmc/waterius/tests/METF/test_crc.py

# -*- coding: utf-8 -*-
import unittest
from metf_python_client import str2hex

from waterius import dallas_crc8


ESP_HOST = '192.168.3.46'


class TestDallasCRC8(unittest.TestCase):

    def test_crc(self):
        self.assertEqual(str2hex('EB'), chr(dallas_crc8(str2hex('3132'), 2)))
        self.assertEqual(str2hex('31'), chr(dallas_crc8(str2hex('0000145D6E0F01'), 7)))


if __name__ == '__main__':
    unittest.main()
